3DO-EU/nozzle-camera/printers/VzBoT/Upper_duct.3mf

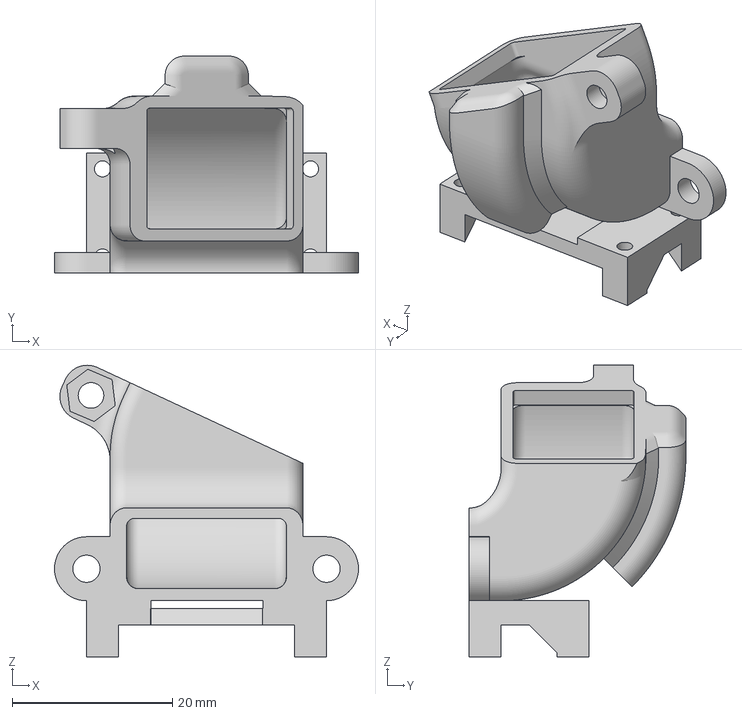
[picture p19: CAD file, 2023-05-12]
printers/VzBoT/Upper_duct.3mf
38.0 x 27.1 x 36.4 mm
