3DO-EU/nozzle-camera/hardware/3NC_mount_geometry_V2.step

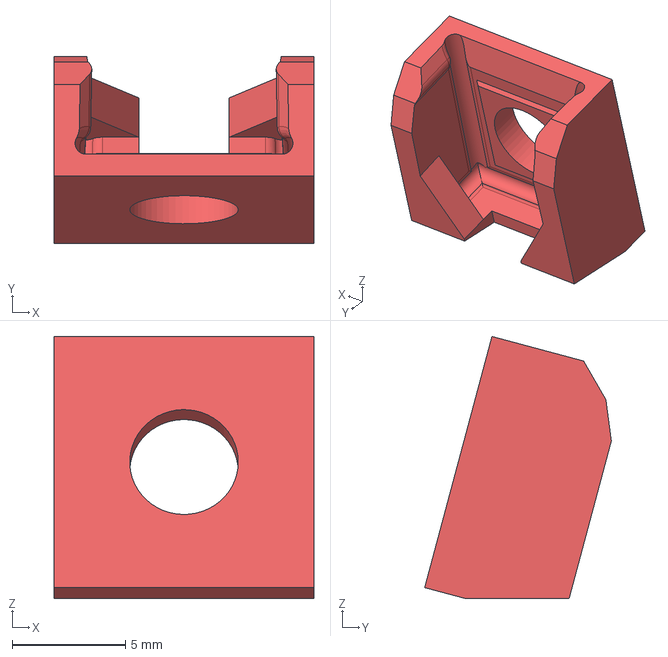
[picture p20: CAD file, 2023-01-15]
hardware/3NC_mount_geometry_V2.step
11.5 x 8.26 x 11.6 mm
