3DO-EU/nozzle-camera/printers/EVA_3/3DO EVA vulcano duct nozzle cam V2.3mf

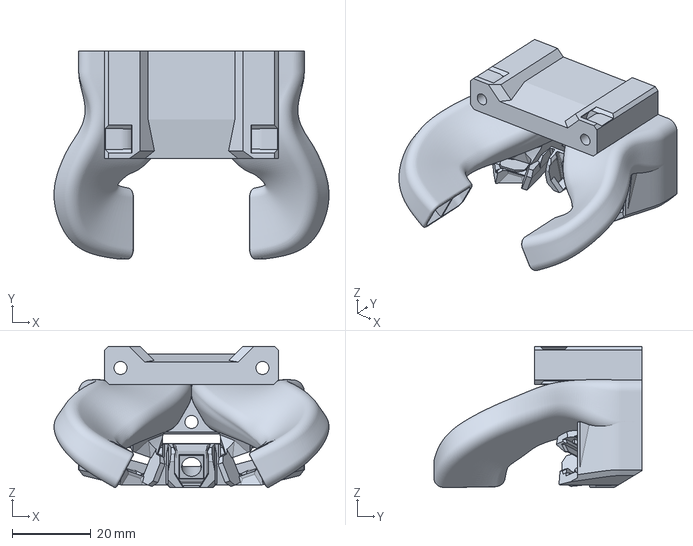
[picture p21: CAD file, 2023-02-06]
printers/EVA_3/3DO EVA vulcano duct nozzle cam V2.3mf
69.7 x 52.7 x 35.9 mm
