3DO-EU/nozzle-camera/printers/Voron_Stealthburner/STLs/Misc/lgx-lite_pcb_taping_jig.stl

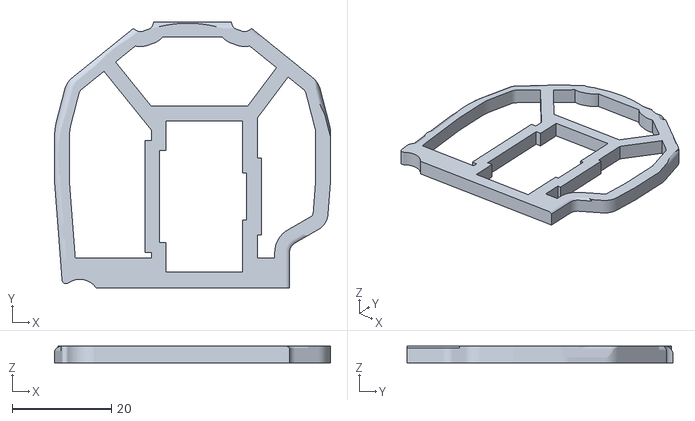
[picture p23: CAD file, 2023-01-19]
printers/Voron_Stealthburner/STLs/Misc/lgx-lite_pcb_taping_jig.stl
55.6 x 53.6 x 3.40
