3DO-EU/nozzle-camera/printers/VzBoT/CPAP_upper_duct.3mf

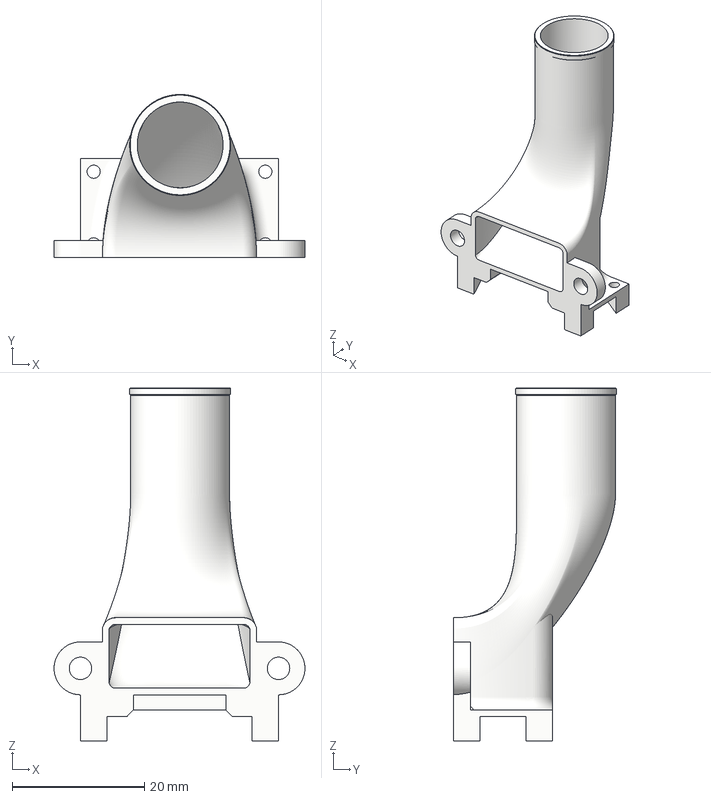
[picture p25: CAD file, 2023-05-12]
printers/VzBoT/CPAP_upper_duct.3mf
38.0 x 24.7 x 53.5 mm
