3DO-EU/nozzle-camera/printers/EVA_3/3DO nozzle cam back cover.3mf

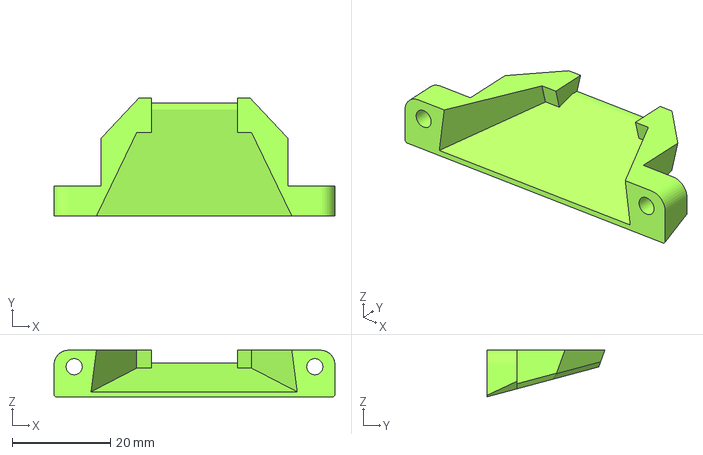
[picture p26: CAD file, 2023-02-06]
printers/EVA_3/3DO nozzle cam back cover.3mf
57.2 x 24.0 x 9.52 mm
