3DO-EU/nozzle-camera/printers/Voron_Stealthburner/CAD/Misc/PCB_mount_SB.step

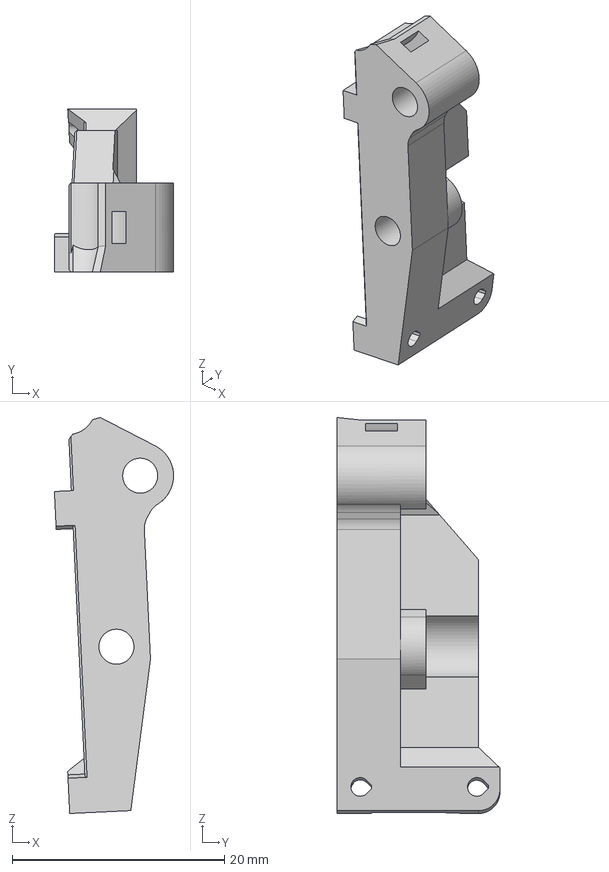
[picture p27: CAD file, 2023-01-15]
printers/Voron_Stealthburner/CAD/Misc/PCB_mount_SB.step
11.2 x 15.4 x 37.3 mm
