3DO-EU/nozzle-camera/printers/Voron_Stealthburner/STLs/Standard/Cam_mount_SB-V.stl

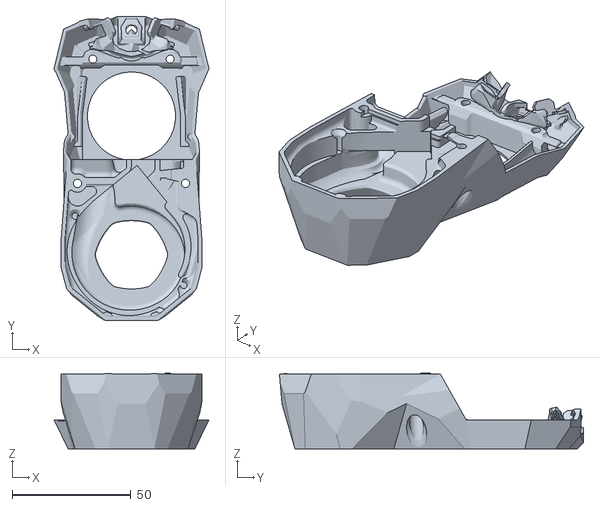
[picture p28: CAD file, 2023-01-23]
printers/Voron_Stealthburner/STLs/Standard/Cam_mount_SB-V.stl
65.1 x 127.8 x 31.8
