3DO-EU/nozzle-camera/printers/VzBoT/Cam_Goliath_duct.3mf

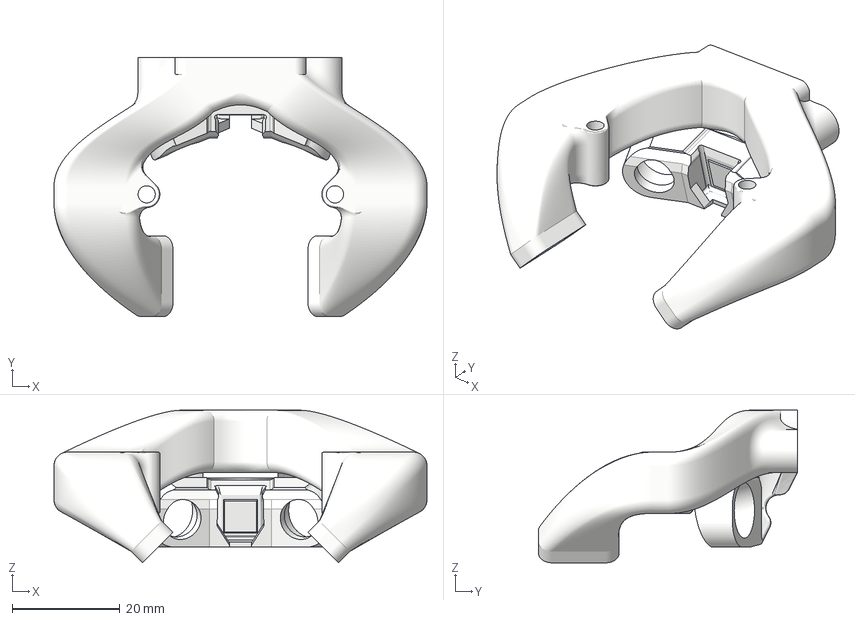
[picture p29: CAD file, 2023-05-12]
printers/VzBoT/Cam_Goliath_duct.3mf
69.3 x 48.1 x 28.4 mm
