3DO-EU/nozzle-camera/printers/EVA_3/3DO nozzle cam pcb cover V2.3mf

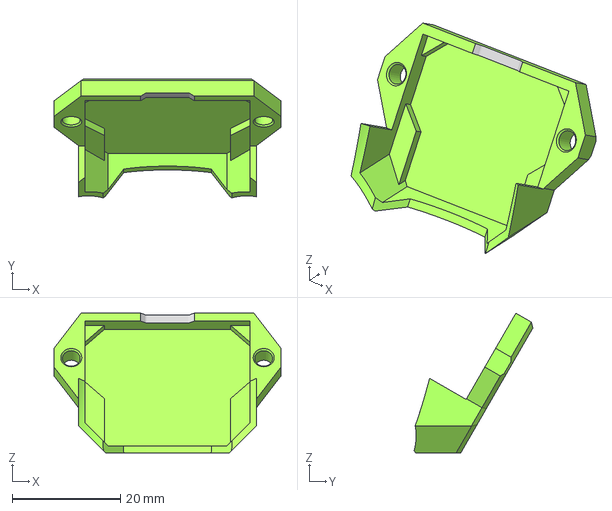
[picture p30: CAD file, 2023-02-06]
printers/EVA_3/3DO nozzle cam pcb cover V2.3mf
42.0 x 22.0 x 25.8 mm
