3DO-EU/nozzle-camera/printers/Prusa I3 MK3/Option A Nozzle-Cam 3DO 4K BoxHolder V9.3mf

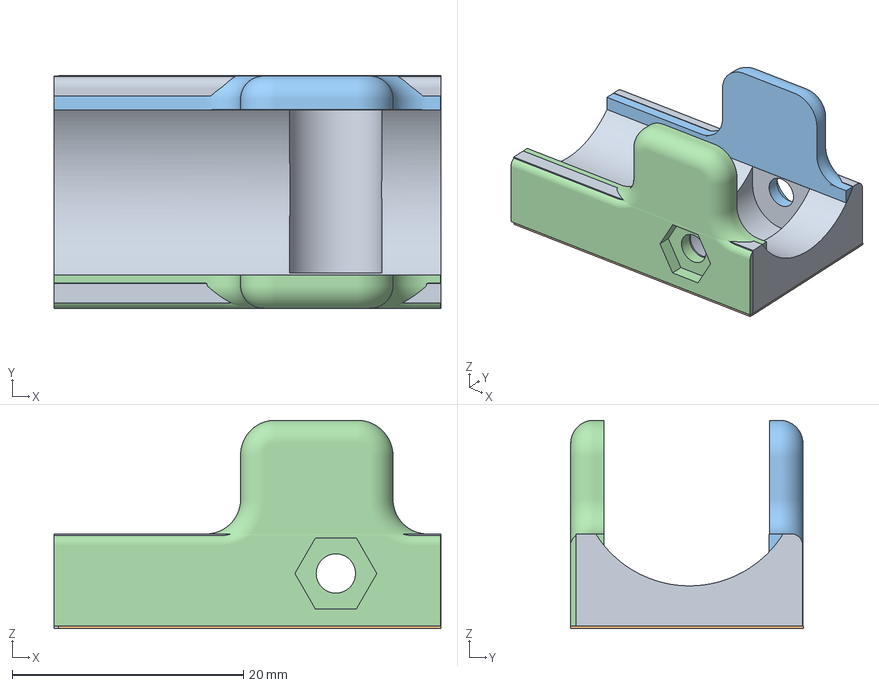
[picture p31: CAD file, 2023-05-12]
printers/Prusa I3 MK3/Option A Nozzle-Cam 3DO 4K BoxHolder V9.3mf
33.5 x 20.2 x 18.0 mm
K_rper_07
Boden
KlammerNeu
KlammerNeu_(1)
