3DO-EU/nozzle-camera/printers/Voron_Stealthburner/CAD/Misc/PCB_mount_SB_Magnum_plus-UHF.step

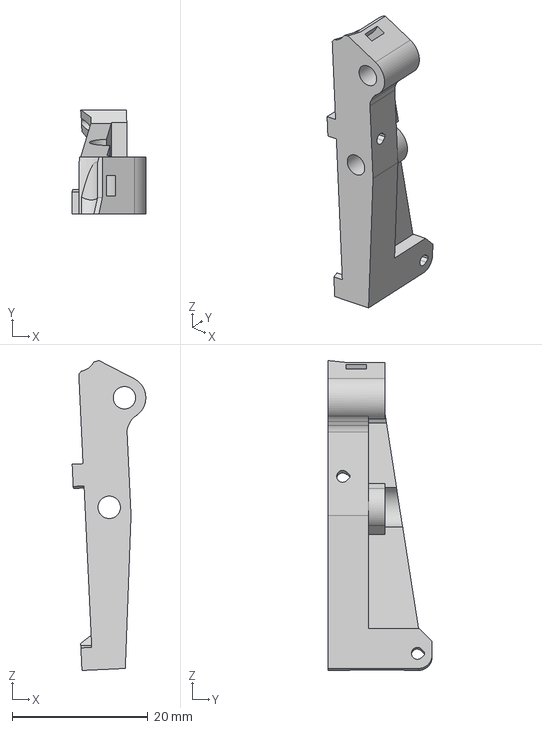
[picture p32: CAD file, 2023-01-15]
printers/Voron_Stealthburner/CAD/Misc/PCB_mount_SB_Magnum_plus-UHF.step
10.8 x 15.4 x 45.6 mm
