3DO-EU/nozzle-camera/printers/VzBoT/Spacer x 2.3mf

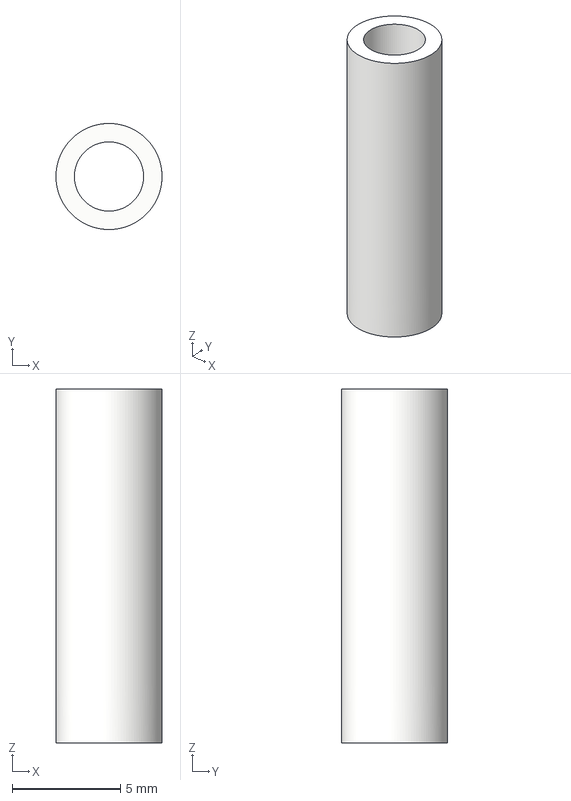
[picture p33: CAD file, 2023-05-12]
printers/VzBoT/Spacer x 2.3mf
4.90 x 4.90 x 16.4 mm
