3DO-EU/nozzle-camera/printers/VzBoT/PCB cover.3mf

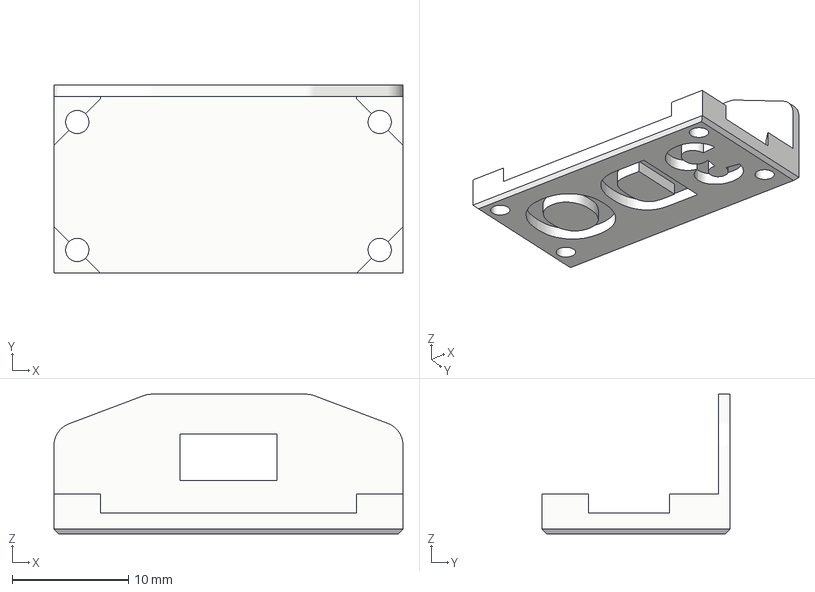
[picture p34: CAD file, 2023-05-12]
printers/VzBoT/PCB cover.3mf
30.0 x 16.2 x 12.0 mm
