3DO-EU/nozzle-camera/printers/Prusa I3 MK3/Nozzle Cam 3DO PCB Top V9.3mf

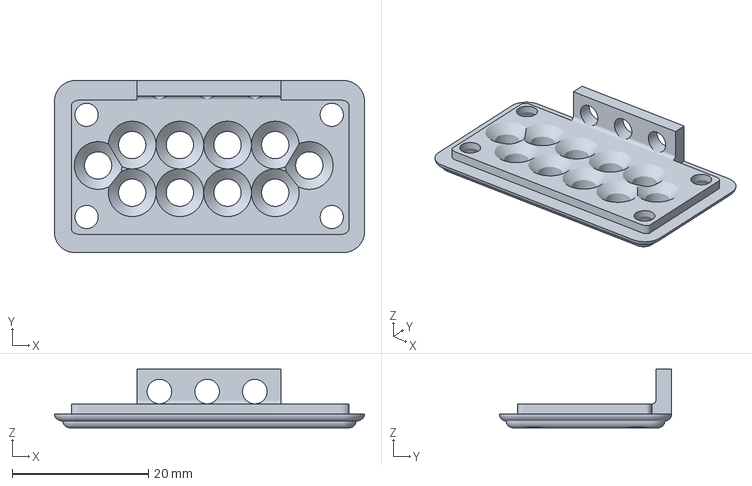
[picture p35: CAD file, 2023-05-12]
printers/Prusa I3 MK3/Nozzle Cam 3DO PCB Top V9.3mf
45.5 x 25.3 x 8.60 mm
