3DO-EU/nozzle-camera/printers/Prusa I3 MK3/Option B Nozzle Cam 3DO PCB Kabelhalter V13.3mf

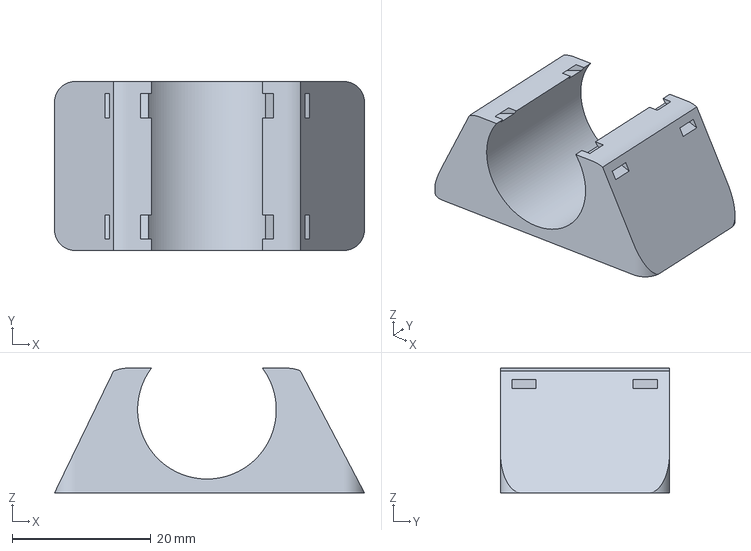
[picture p36: CAD file, 2023-05-12]
printers/Prusa I3 MK3/Option B Nozzle Cam 3DO PCB Kabelhalter V13.3mf
44.7 x 24.4 x 18.0 mm
