3DO-EU/nozzle-camera/printers/Prusa I3 MK3/Nozzle-Cam 3DO 4K V13 LED Pearl Blende PRINT.3mf

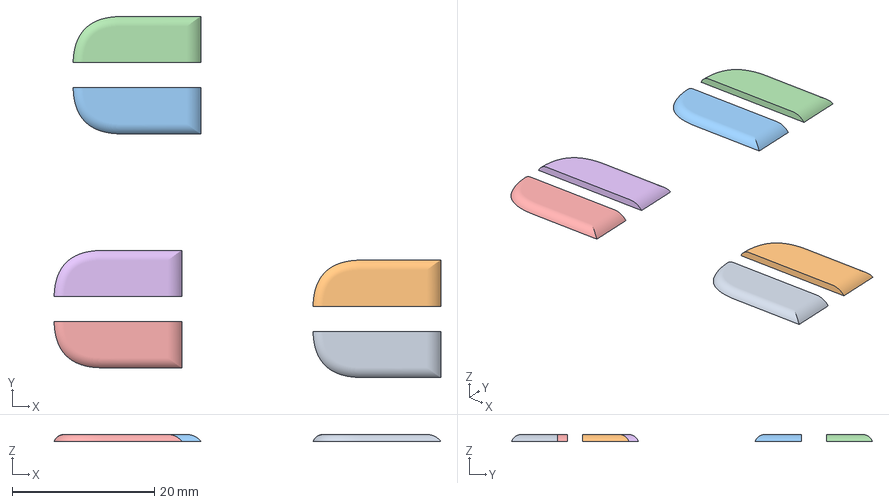
[picture p37: CAD file, 2023-05-12]
printers/Prusa I3 MK3/Nozzle-Cam 3DO 4K V13 LED Pearl Blende PRINT.3mf
54.4 x 50.7 x 1 mm
Blende_L x 3
Blende_R x 3
