3DO-EU/nozzle-camera/printers/Prusa I3 MK3/Nozzle-Cam 3DO 4K V13 LED Pearl AB.3mf

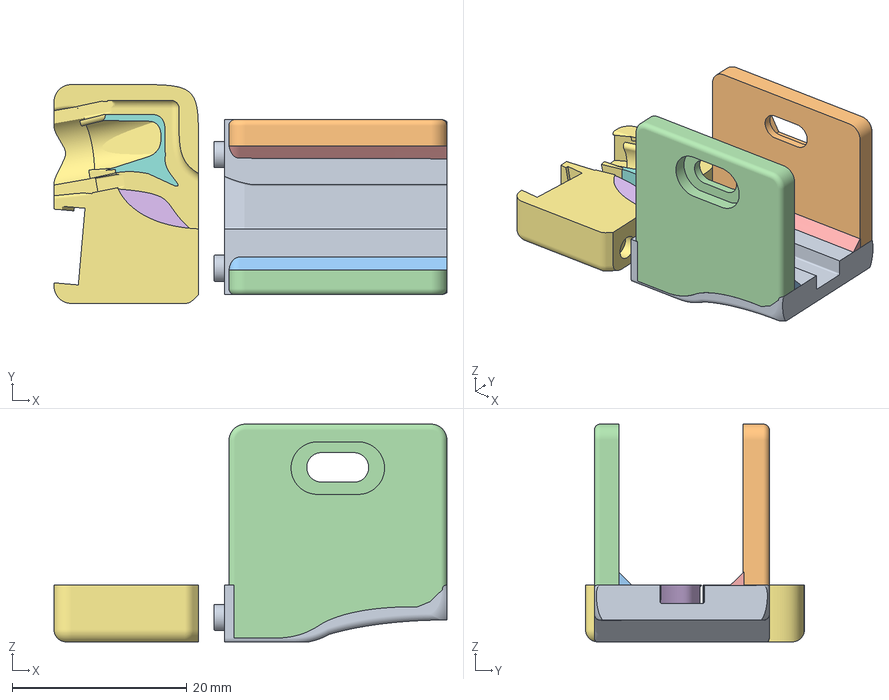
[picture p38: CAD file, 2023-05-12]
printers/Prusa I3 MK3/Nozzle-Cam 3DO 4K V13 LED Pearl AB.3mf
44.9 x 25.0 x 24.9 mm
Kamera__(2)*
Klammer_Links_(2)
Winkel
Klammer_Links_(1)
Winkel_(2)
K_rper_15
Cambody
K_rper_16
