3DO-EU/nozzle-camera/printers/Prusa I3 MK3/Option B Nozzle Cam 3DO V13 All Parts Print.3mf

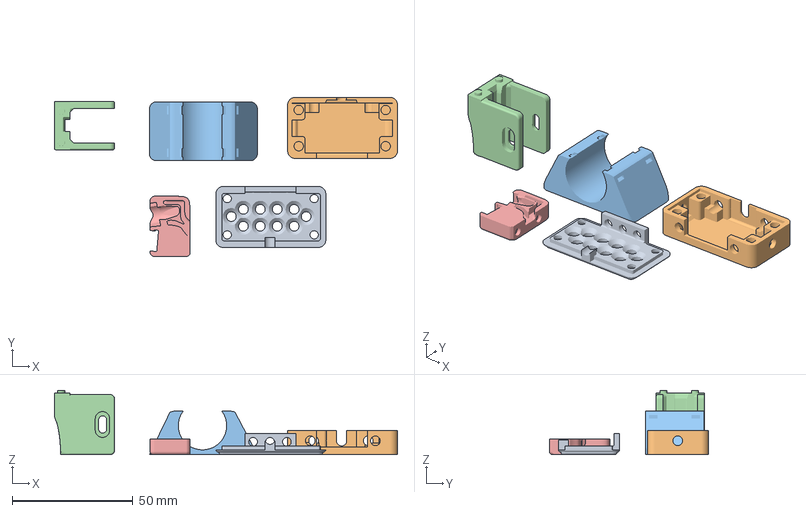
[picture p39: CAD file, 2023-05-12]
printers/Prusa I3 MK3/Option B Nozzle Cam 3DO V13 All Parts Print.3mf
142.0 x 65.9 x 26.6 mm
Nozzle Cam 3DO PCB Deckel V13.stl
Nozzle Cam 3DO PCB Case V13.stl
Nozzle Cam 3DO PCB Kabelhalter V13.stl
Nozzle-Cam 3DO 4K V13 LED Pearl B
Nozzle-Cam 3DO 4K V13 LED Pearl A
