3DO-EU/nozzle-camera/printers/Prusa I3 MK3/Nozzle-Cam 3DO 4K V13 LED Pearl B.3mf

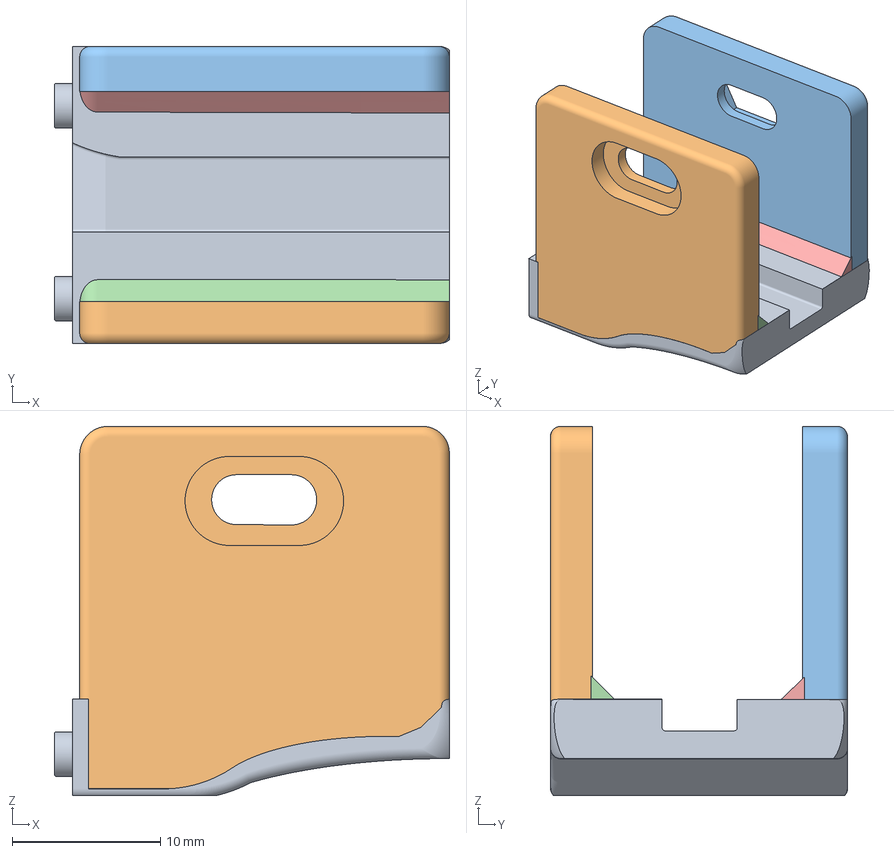
[picture p40: CAD file, 2023-05-12]
printers/Prusa I3 MK3/Nozzle-Cam 3DO 4K V13 LED Pearl B.3mf
26.6 x 20.0 x 24.9 mm
Kamera__(2)*
Klammer_Links_(1)
Klammer_Links_(2)
Winkel
Winkel_(2)
