3DO-EU/nozzle-camera/printers/Prusa I3 MK3/Nozzle Cam 3DO Komplett V11 PRINT.3mf

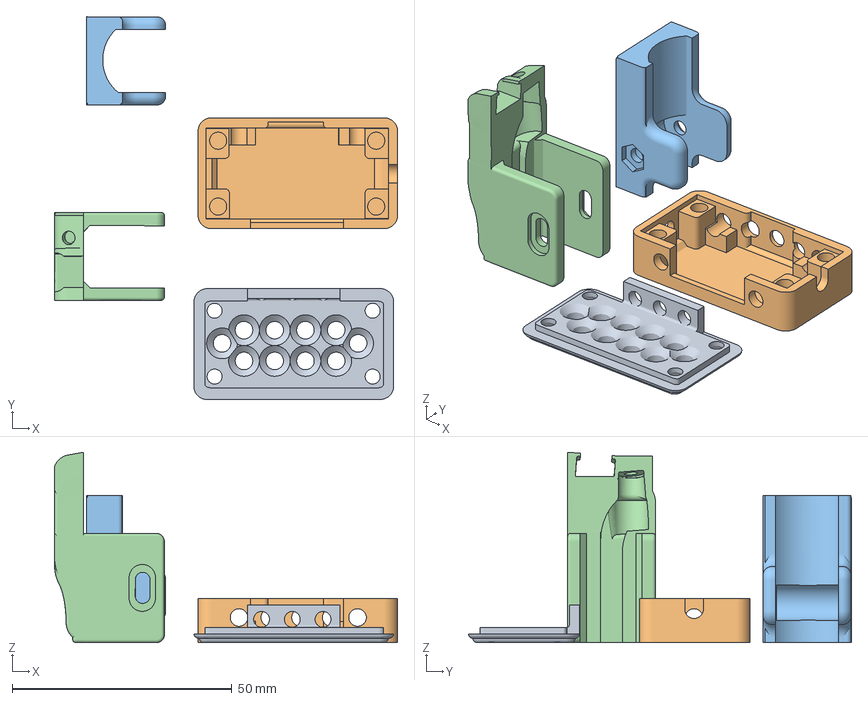
[picture p41: CAD file, 2023-05-12]
printers/Prusa I3 MK3/Nozzle Cam 3DO Komplett V11 PRINT.3mf
78.2 x 87.2 x 43.4 mm
Nozzle Cam 3DO PCB Top V9
Nozzle Cam 3DO PCB Case V9
Nozzle-Cam 3DO 4K BoxHolder V9
Nozzle-Cam 3DO 4K V11
