3DO-EU/nozzle-camera/printers/Prusa I3 MK3/Nozzle-Cam 3DO 4K V13 LED Pearl Blende.stl

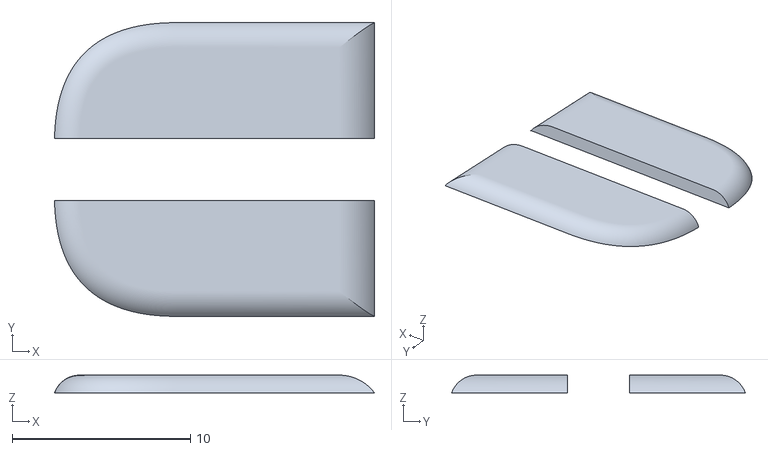
[picture p42: CAD file, 2023-05-12]
printers/Prusa I3 MK3/Nozzle-Cam 3DO 4K V13 LED Pearl Blende.stl
18.0 x 16.5 x 1.00
