3DO-EU/nozzle-camera/printers/Prusa I3 MK3/Option B Nozzle Cam 3DO PCB Deckel   V13.3mf

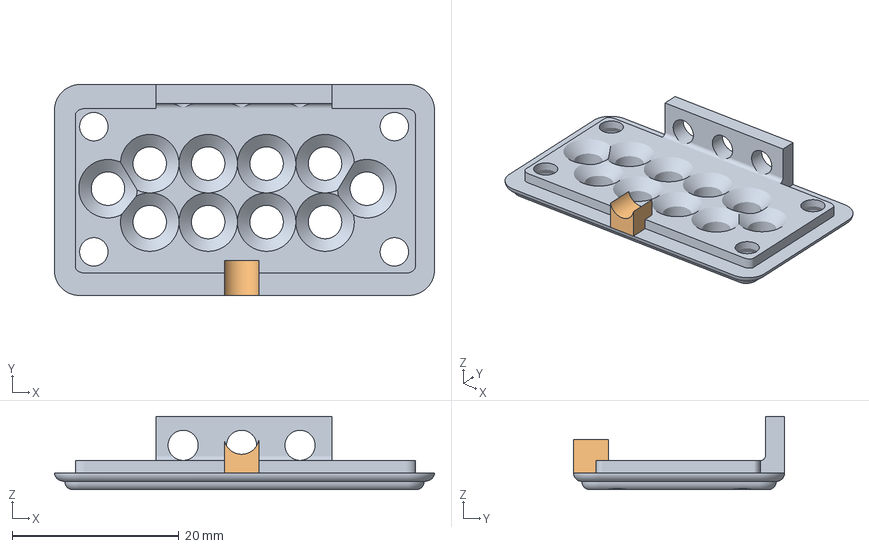
[picture p43: CAD file, 2023-05-12]
printers/Prusa I3 MK3/Option B Nozzle Cam 3DO PCB Deckel V13.3mf
45.5 x 25.3 x 8.80 mm
Deckel1
K_rper_12
