3DO-EU/nozzle-camera/printers/Voron_Stealthburner/images/Showroom/Cam_mount_SB_Hex_knomi.png

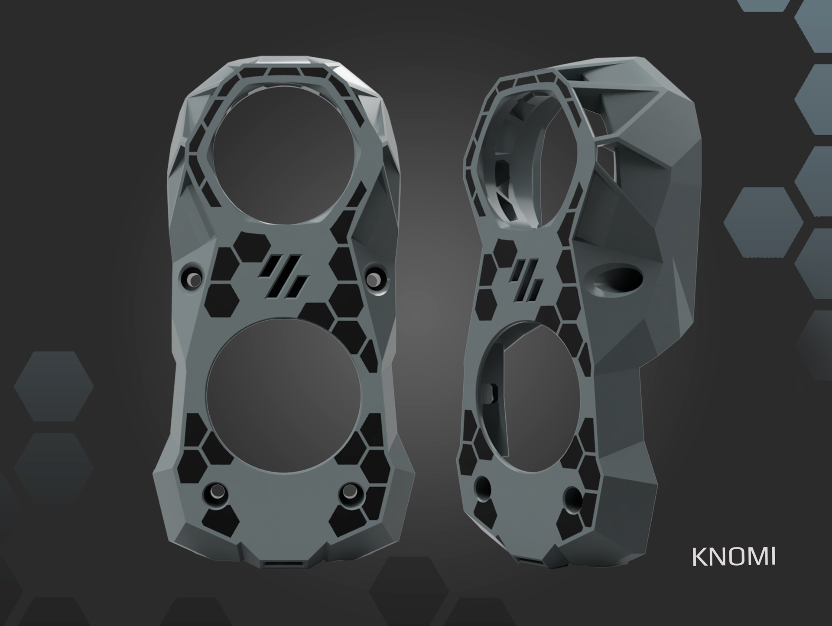
printers/Voron_Stealthburner/images/Showroom/Cam_mount_SB_Hex_knomi.png
