3DO-EU/nozzle-camera/printers/Voron_Stealthburner/images/Showroom/Cam_mount_SB_UHF-HEX_Front_view.png

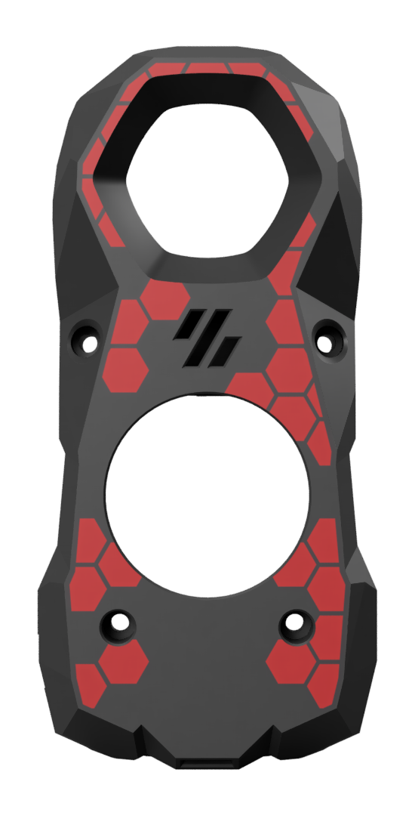
printers/Voron_Stealthburner/images/Showroom/Cam_mount_SB_UHF-HEX_Front_view.png
